feiticeir0/ai-candy-dispenser/assets/Candy_Dispenser.jpg

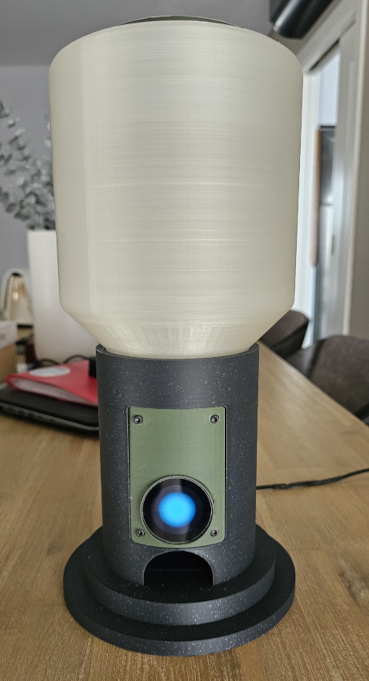
assets/Candy_Dispenser.jpg
