feiticeir0/ai-candy-dispenser/assets/candyDispenser.png

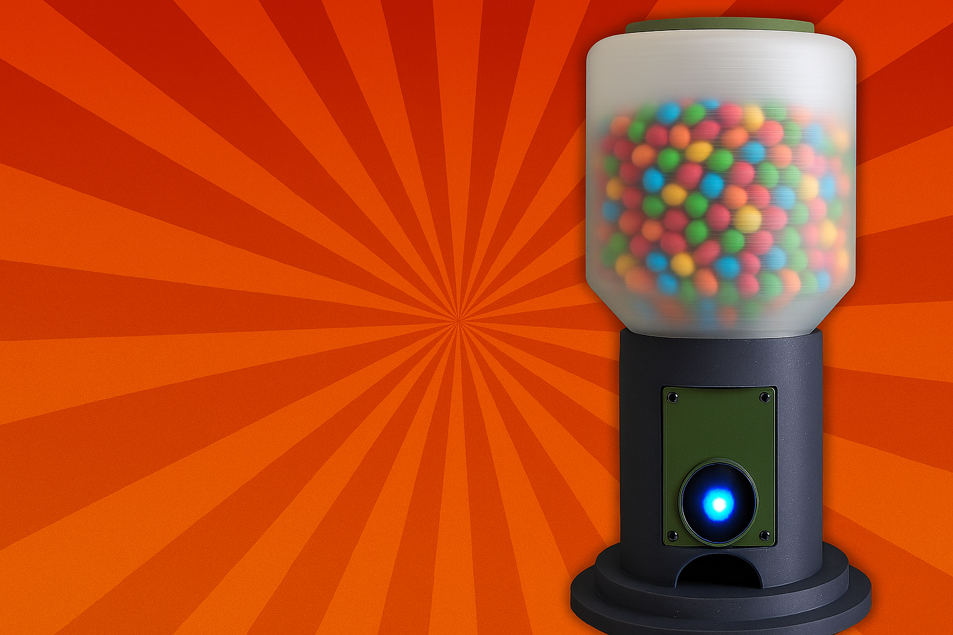
assets/candyDispenser.png
