feiticeir0/ai-candy-dispenser/Arduino/files/cookie.h

/*
 * Nome do ficheiro: cookie.h
 * Autor: Bruno Ricardo Santos - feiticeir0@whatgeek.com.pt (c) 2025
 * Licença: GNU General Public License v3.0 (GPLv3)
 *
 * Este programa é software livre: pode redistribuí-lo e/ou modificá-lo
 * sob os termos da Licença Pública Geral GNU conforme publicada pela Free Software Foundation,
 * quer a versão 3 da Licença, ou (a teu critério) qualquer versão posterior.
 *
 * Este programa é distribuído na expectativa de que seja útil,
 * mas SEM QUALQUER GARANTIA; sem mesmo a garantia implícita
 * de COMERCIALIZAÇÃO ou ADEQUAÇÃO A UM DETERMINADO FIM.
 * Veja a Licença Pública Geral GNU para mais detalhes.
 *
 * Deverás ter recebido uma cópia da Licença Pública Geral GNU
 * juntamente com este programa. Se não, veja <https://www.gnu.org/licenses/>.
 */

// array size is 6202
static const byte cookie[] PROGMEM  = {
  0x89, 0x50, 0x4e, 0x47, 0x0d, 0x0a, 0x1a, 0x0a, 0x00, 0x00, 0x00, 0x0d, 0x49, 0x48, 0x44, 0x52, 
  0x00, 0x00, 0x00, 0x44, 0x00, 0x00, 0x00, 0x45, 0x08, 0x06, 0x00, 0x00, 0x00, 0xf3, 0x4f, 0x40, 
  0x17, 0x00, 0x00, 0x00, 0x01, 0x73, 0x52, 0x47, 0x42, 0x01, 0xd9, 0xc9, 0x2c, 0x7f, 0x00, 0x00, 
  0x00, 0x04, 0x67, 0x41, 0x4d, 0x41, 0x00, 0x00, 0xb1, 0x8f, 0x0b, 0xfc, 0x61, 0x05, 0x00, 0x00, 
  0x00, 0x20, 0x63, 0x48, 0x52, 0x4d, 0x00, 0x00, 0x7a, 0x26, 0x00, 0x00, 0x80, 0x84, 0x00, 0x00, 
  0xfa, 0x00, 0x00, 0x00, 0x80, 0xe8, 0x00, 0x00, 0x75, 0x30, 0x00, 0x00, 0xea, 0x60, 0x00, 0x00, 
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
  0xdf, 0x91, 0xfc, 0x53, 0x4a, 0x7f, 0x87, 0x08, 0x4d, 0x59, 0x9a, 0xd6, 0xf1, 0x39, 0x34, 0x85, 
  0xb4, 0xdc, 0xe8, 0xec, 0x8c, 0x8b, 0xef, 0x3f, 0x5b, 0xc7, 0xe6, 0x01, 0x03, 0xfd, 0x1d, 0x2a, 
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
};
