feiticeir0/ai-candy-dispenser/Arduino/files/no_cookies.h

/*
 * Nome do ficheiro: no_cookies.h
 * Autor: Bruno Ricardo Santos - feiticeir0@whatgeek.com.pt (c) 2025
 * Licença: GNU General Public License v3.0 (GPLv3)
 *
 * Este programa é software livre: pode redistribuí-lo e/ou modificá-lo
 * sob os termos da Licença Pública Geral GNU conforme publicada pela Free Software Foundation,
 * quer a versão 3 da Licença, ou (a teu critério) qualquer versão posterior.
 *
 * Este programa é distribuído na expectativa de que seja útil,
 * mas SEM QUALQUER GARANTIA; sem mesmo a garantia implícita
 * de COMERCIALIZAÇÃO ou ADEQUAÇÃO A UM DETERMINADO FIM.
 * Veja a Licença Pública Geral GNU para mais detalhes.
 *
 * Deverás ter recebido uma cópia da Licença Pública Geral GNU
 * juntamente com este programa. Se não, veja <https://www.gnu.org/licenses/>.
 */
 
// array size is 63781
static const byte no_cookies[] PROGMEM  = {
  0x89, 0x50, 0x4e, 0x47, 0x0d, 0x0a, 0x1a, 0x0a, 0x00, 0x00, 0x00, 0x0d, 0x49, 0x48, 0x44, 0x52, 
  0x00, 0x00, 0x00, 0xf0, 0x00, 0x00, 0x00, 0xf0, 0x08, 0x06, 0x00, 0x00, 0x00, 0x3e, 0x55, 0xe9, 
  0x92, 0x00, 0x00, 0x00, 0x01, 0x73, 0x52, 0x47, 0x42, 0x01, 0xd9, 0xc9, 0x2c, 0x7f, 0x00, 0x00, 
  0x00, 0x04, 0x67, 0x41, 0x4d, 0x41, 0x00, 0x00, 0xb1, 0x8f, 0x0b, 0xfc, 0x61, 0x05, 0x00, 0x00, 
  0x00, 0x20, 0x63, 0x48, 0x52, 0x4d, 0x00, 0x00, 0x7a, 0x26, 0x00, 0x00, 0x80, 0x84, 0x00, 0x00, 
  0xfa, 0x00, 0x00, 0x00, 0x80, 0xe8, 0x00, 0x00, 0x75, 0x30, 0x00, 0x00, 0xea, 0x60, 0x00, 0x00, 
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
  0x6f, 0x60, 0x67, 0xe3, 0xb2, 0xb6, 0xb4, 0x23, 0xb8, 0x67, 0xb7, 0x33, 0x17, 0x93, 0x9a, 0x5d, 
  0xd7, 0xd6, 0x7d, 0xa3, 0x2c, 0x98, 0x72, 0xbb, 0x87, 0xad, 0xba, 0x28, 0xf4, 0xc5, 0xc5, 0x5c, 
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
};
